ATmega8/kiterf/project/code/ESP32/Demo/components/dsp/include/dsp_math.h

#pragma once

/* Compiler specific diagnostic adjustment */
#if   defined ( __CC_DSP )

#elif defined ( __DSPCC_VERSION ) && ( __DSPCC_VERSION >= 6010050 )

#elif defined ( __GNUC__ )
#pragma GCC diagnostic push
#pragma GCC diagnostic ignored "-Wsign-conversion"
#pragma GCC diagnostic ignored "-Wconversion"
#pragma GCC diagnostic ignored "-Wunused-parameter"

#elif defined ( __ICCDSP__ )

#elif defined ( __TI_DSP__ )

#elif defined ( __CSMC__ )

#elif defined ( __TASKING__ )

#else
#error Unknown compiler
#endif

#include "string.h"
#include "math.h"
#include "stdint.h"
#ifdef   __cplusplus
extern "C"
{
#endif


/**
 * @brief Macros required for reciprocal calculation in Normalized LMS
 */


#define INDEX_MASK         0x0000003F
#ifndef PI
#define PI               3.14159265358979f
#endif

/**
 * @brief Macros required for SINE and COSINE Fast math approximations
 */

#define FAST_MATH_TABLE_SIZE  512


/**
 * @brief Error status returned by some functions in the library.
 */

typedef enum {
    dsp_MATH_SUCCESS = 0,                /**< No error */
    dsp_MATH_ARGUMENT_ERROR = -1,        /**< One or more arguments are incorrect */
    dsp_MATH_LENGTH_ERROR = -2,          /**< Length of data buffer is incorrect */
    dsp_MATH_SIZE_MISMATCH = -3,         /**< Size of matrices is not compatible with the operation. */
    dsp_MATH_NANINF = -4,                /**< Not-a-number (NaN) or infinity is generated */
    dsp_MATH_SINGULAR = -5,              /**< Generated by matrix inversion if the input matrix is singular and cannot be inverted. */
    dsp_MATH_TEST_FAILURE = -6           /**< Test Failed  */
} dsp_status;


/**
 * @brief 32-bit floating-point type definition.
 */
typedef float float32_t;

/**
 * @brief Instance structure for the floating-point FIR filter.
 */
typedef struct {
    uint16_t numTaps;     /**< number of filter coefficients in the filter. */
    float32_t *pState;    /**< points to the state variable array. The array is of length numTaps+blockSize-1. */
    float32_t *pCoeffs;   /**< points to the coefficient array. The array is of length numTaps. */
} dsp_fir_instance_f32;





/**
 * @brief Processing function for the floating-point FIR filter.
 * @param[in]  S          points to an instance of the floating-point FIR structure.
 * @param[in]  pSrc       points to the block of input data.
 * @param[out] pDst       points to the block of output data.
 * @param[in]  blockSize  number of samples to process.
 */
void dsp_fir_f32(
    const dsp_fir_instance_f32 *S,
    float32_t *pSrc,
    float32_t *pDst,
    uint32_t blockSize);


/**
 * @brief  Initialization function for the floating-point FIR filter.
 * @param[in,out] S          points to an instance of the floating-point FIR filter structure.
 * @param[in]     numTaps    Number of filter coefficients in the filter.
 * @param[in]     pCoeffs    points to the filter coefficients.
 * @param[in]     pState     points to the state buffer.
 * @param[in]     blockSize  number of samples that are processed at a time.
 */
void dsp_fir_init_f32(
    dsp_fir_instance_f32 *S,
    uint16_t numTaps,
    float32_t *pCoeffs,
    float32_t *pState,
    uint32_t blockSize);




/**
 * @brief Instance structure for the floating-point Biquad cascade filter.
 */
typedef struct {
    uint32_t numStages;      /**< number of 2nd order stages in the filter.  Overall order is 2*numStages. */
    float32_t *pState;       /**< Points to the array of state coefficients.  The array is of length 4*numStages. */
    float32_t *pCoeffs;      /**< Points to the array of coefficients.  The array is of length 5*numStages. */
} dsp_biquad_casd_df1_inst_f32;





/**
 * @brief Processing function for the floating-point Biquad cascade filter.
 * @param[in]  S          points to an instance of the floating-point Biquad cascade structure.
 * @param[in]  pSrc       points to the block of input data.
 * @param[out] pDst       points to the block of output data.
 * @param[in]  blockSize  number of samples to process.
 */
void dsp_biquad_cascade_df1_f32(
    const dsp_biquad_casd_df1_inst_f32 *S,
    float32_t *pSrc,
    float32_t *pDst,
    uint32_t blockSize);


/**
 * @brief  Initialization function for the floating-point Biquad cascade filter.
 * @param[in,out] S          points to an instance of the floating-point Biquad cascade structure.
 * @param[in]     numStages  number of 2nd order stages in the filter.
 * @param[in]     pCoeffs    points to the filter coefficients.
 * @param[in]     pState     points to the state buffer.
 */
void dsp_biquad_cascade_df1_init_f32(
    dsp_biquad_casd_df1_inst_f32 *S,
    uint8_t numStages,
    float32_t *pCoeffs,
    float32_t *pState);


/**
 * @brief Instance structure for the floating-point matrix structure.
 */
typedef struct {
    uint16_t numRows;     /**< number of rows of the matrix.     */
    uint16_t numCols;     /**< number of columns of the matrix.  */
    float32_t *pData;     /**< points to the data of the matrix. */
} dsp_matrix_instance_f32;







/**
 * @brief Floating-point matrix addition.
 * @param[in]  pSrcA  points to the first input matrix structure
 * @param[in]  pSrcB  points to the second input matrix structure
 * @param[out] pDst   points to output matrix structure
 * @return     The function returns either
 * <code>dsp_MATH_SIZE_MISMATCH</code> or <code>dsp_MATH_SUCCESS</code> based on the outcome of size checking.
 */
dsp_status dsp_mat_add_f32(
    const dsp_matrix_instance_f32 *pSrcA,
    const dsp_matrix_instance_f32 *pSrcB,
    dsp_matrix_instance_f32 *pDst);





/**
 * @brief Floating-point, complex, matrix multiplication.
 * @param[in]  pSrcA  points to the first input matrix structure
 * @param[in]  pSrcB  points to the second input matrix structure
 * @param[out] pDst   points to output matrix structure
 * @return     The function returns either
 * <code>dsp_MATH_SIZE_MISMATCH</code> or <code>dsp_MATH_SUCCESS</code> based on the outcome of size checking.
 */
dsp_status dsp_mat_cmplx_mult_f32(
    const dsp_matrix_instance_f32 *pSrcA,
    const dsp_matrix_instance_f32 *pSrcB,
    dsp_matrix_instance_f32 *pDst);




/**
 * @brief Floating-point matrix transpose.
 * @param[in]  pSrc  points to the input matrix
 * @param[out] pDst  points to the output matrix
 * @return    The function returns either  <code>dsp_MATH_SIZE_MISMATCH</code>
 * or <code>dsp_MATH_SUCCESS</code> based on the outcome of size checking.
 */
dsp_status dsp_mat_trans_f32(
    const dsp_matrix_instance_f32 *pSrc,
    dsp_matrix_instance_f32 *pDst);





/**
 * @brief Floating-point matrix multiplication
 * @param[in]  pSrcA  points to the first input matrix structure
 * @param[in]  pSrcB  points to the second input matrix structure
 * @param[out] pDst   points to output matrix structure
 * @return     The function returns either
 * <code>dsp_MATH_SIZE_MISMATCH</code> or <code>dsp_MATH_SUCCESS</code> based on the outcome of size checking.
 */
dsp_status dsp_mat_mult_f32(
    const dsp_matrix_instance_f32 *pSrcA,
    const dsp_matrix_instance_f32 *pSrcB,
    dsp_matrix_instance_f32 *pDst);





/**
 * @brief Floating-point matrix subtraction
 * @param[in]  pSrcA  points to the first input matrix structure
 * @param[in]  pSrcB  points to the second input matrix structure
 * @param[out] pDst   points to output matrix structure
 * @return     The function returns either
 * <code>dsp_MATH_SIZE_MISMATCH</code> or <code>dsp_MATH_SUCCESS</code> based on the outcome of size checking.
 */
dsp_status dsp_mat_sub_f32(
    const dsp_matrix_instance_f32 *pSrcA,
    const dsp_matrix_instance_f32 *pSrcB,
    dsp_matrix_instance_f32 *pDst);




/**
 * @brief Floating-point matrix scaling.
 * @param[in]  pSrc   points to the input matrix
 * @param[in]  scale  scale factor
 * @param[out] pDst   points to the output matrix
 * @return     The function returns either
 * <code>dsp_MATH_SIZE_MISMATCH</code> or <code>dsp_MATH_SUCCESS</code> based on the outcome of size checking.
 */
dsp_status dsp_mat_scale_f32(
    const dsp_matrix_instance_f32 *pSrc,
    float32_t scale,
    dsp_matrix_instance_f32 *pDst);





/**
 * @brief  Floating-point matrix initialization.
 * @param[in,out] S         points to an instance of the floating-point matrix structure.
 * @param[in]     nRows     number of rows in the matrix.
 * @param[in]     nColumns  number of columns in the matrix.
 * @param[in]     pData     points to the matrix data array.
 */
void dsp_mat_init_f32(
    dsp_matrix_instance_f32 *S,
    uint16_t nRows,
    uint16_t nColumns,
    float32_t *pData);




/**
 * @brief Instance structure for the floating-point PID Control.
 */
typedef struct {
    float32_t A0;          /**< The derived gain, A0 = Kp + Ki + Kd . */
    float32_t A1;          /**< The derived gain, A1 = -Kp - 2Kd. */
    float32_t A2;          /**< The derived gain, A2 = Kd . */
    float32_t state[3];    /**< The state array of length 3. */
    float32_t Kp;          /**< The proportional gain. */
    float32_t Ki;          /**< The integral gain. */
    float32_t Kd;          /**< The derivative gain. */
} dsp_pid_instance_f32;



/**
 * @brief  Initialization function for the floating-point PID Control.
 * @param[in,out] S               points to an instance of the PID structure.
 * @param[in]     resetStateFlag  flag to reset the state. 0 = no change in state 1 = reset the state.
 */
void dsp_pid_init_f32(
    dsp_pid_instance_f32 *S,
    int32_t resetStateFlag);


/**
 * @brief  Reset function for the floating-point PID Control.
 * @param[in,out] S  is an instance of the floating-point PID Control structure
 */
void dsp_pid_reset_f32(
    dsp_pid_instance_f32 *S);




/**
 * @brief Instance structure for the floating-point Linear Interpolate function.
 */
typedef struct {
    uint32_t nValues;           /**< nValues */
    float32_t x1;               /**< x1 */
    float32_t xSpacing;         /**< xSpacing */
    float32_t *pYData;          /**< pointer to the table of Y values */
} dsp_linear_interp_instance_f32;

/**
 * @brief Instance structure for the floating-point bilinear interpolation function.
 */
typedef struct {
    uint16_t numRows;   /**< number of rows in the data table. */
    uint16_t numCols;   /**< number of columns in the data table. */
    float32_t *pData;   /**< points to the data table. */
} dsp_bilinear_interp_instance_f32;

/**
* @brief Instance structure for the Q31 bilinear interpolation function.
*/










/**
 * @brief Floating-point vector multiplication.
 * @param[in]  pSrcA      points to the first input vector
 * @param[in]  pSrcB      points to the second input vector
 * @param[out] pDst       points to the output vector
 * @param[in]  blockSize  number of samples in each vector
 */
void dsp_mult_f32(
    float32_t *pSrcA,
    float32_t *pSrcB,
    float32_t *pDst,
    uint32_t blockSize);






/**
 * @brief Instance structure for the floating-point CFFT/CIFFT function.
 */
typedef struct {
    uint16_t fftLen;                   /**< length of the FFT. */
    uint8_t ifftFlag;                  /**< flag that selects forward (ifftFlag=0) or inverse (ifftFlag=1) transform. */
    uint8_t bitReverseFlag;            /**< flag that enables (bitReverseFlag=1) or disables (bitReverseFlag=0) bit reversal of output. */
    float32_t *pTwiddle;               /**< points to the Twiddle factor table. */
    uint16_t *pBitRevTable;            /**< points to the bit reversal table. */
    uint16_t twidCoefModifier;         /**< twiddle coefficient modifier that supports different size FFTs with the same twiddle factor table. */
    uint16_t bitRevFactor;             /**< bit reversal modifier that supports different size FFTs with the same bit reversal table. */
    float32_t onebyfftLen;             /**< value of 1/fftLen. */
} dsp_cfft_radix2_instance_f32;

/* Deprecated */
dsp_status dsp_cfft_radix2_init_f32(
    dsp_cfft_radix2_instance_f32 *S,
    uint16_t fftLen,
    uint8_t ifftFlag,
    uint8_t bitReverseFlag);

/* Deprecated */
void dsp_cfft_radix2_f32(
    const dsp_cfft_radix2_instance_f32 *S,
    float32_t *pSrc);

/**
 * @brief Instance structure for the floating-point CFFT/CIFFT function.
 */
typedef struct {
    uint16_t fftLen;                   /**< length of the FFT. */
    uint8_t ifftFlag;                  /**< flag that selects forward (ifftFlag=0) or inverse (ifftFlag=1) transform. */
    uint8_t bitReverseFlag;            /**< flag that enables (bitReverseFlag=1) or disables (bitReverseFlag=0) bit reversal of output. */
    float32_t *pTwiddle;               /**< points to the Twiddle factor table. */
    uint16_t *pBitRevTable;            /**< points to the bit reversal table. */
    uint16_t twidCoefModifier;         /**< twiddle coefficient modifier that supports different size FFTs with the same twiddle factor table. */
    uint16_t bitRevFactor;             /**< bit reversal modifier that supports different size FFTs with the same bit reversal table. */
    float32_t onebyfftLen;             /**< value of 1/fftLen. */
} dsp_cfft_radix4_instance_f32;

/* Deprecated */
dsp_status dsp_cfft_radix4_init_f32(
    dsp_cfft_radix4_instance_f32 *S,
    uint16_t fftLen,
    uint8_t ifftFlag,
    uint8_t bitReverseFlag);

/* Deprecated */
void dsp_cfft_radix4_f32(
    const dsp_cfft_radix4_instance_f32 *S,
    float32_t *pSrc);


/**
 * @brief Instance structure for the floating-point CFFT/CIFFT function.
 */
typedef struct {
    uint16_t fftLen;                   /**< length of the FFT. */
    const float32_t *pTwiddle;         /**< points to the Twiddle factor table. */
    const uint16_t *pBitRevTable;      /**< points to the bit reversal table. */
    uint16_t bitRevLength;             /**< bit reversal table length. */
} dsp_cfft_instance_f32;

void dsp_cfft_f32(
    const dsp_cfft_instance_f32 *S,
    float32_t *p1,
    uint8_t ifftFlag,
    uint8_t bitReverseFlag);





/**
 * @brief Instance structure for the floating-point RFFT/RIFFT function.
 */
typedef struct {
    uint32_t fftLenReal;                        /**< length of the real FFT. */
    uint16_t fftLenBy2;                         /**< length of the complex FFT. */
    uint8_t ifftFlagR;                          /**< flag that selects forward (ifftFlagR=0) or inverse (ifftFlagR=1) transform. */
    uint8_t bitReverseFlagR;                    /**< flag that enables (bitReverseFlagR=1) or disables (bitReverseFlagR=0) bit reversal of output. */
    uint32_t twidCoefRModifier;                     /**< twiddle coefficient modifier that supports different size FFTs with the same twiddle factor table. */
    float32_t *pTwiddleAReal;                   /**< points to the real twiddle factor table. */
    float32_t *pTwiddleBReal;                   /**< points to the imag twiddle factor table. */
    dsp_cfft_radix4_instance_f32 *pCfft;        /**< points to the complex FFT instance. */
} dsp_rfft_instance_f32;

dsp_status dsp_rfft_init_f32(
    dsp_rfft_instance_f32 *S,
    dsp_cfft_radix4_instance_f32 *S_CFFT,
    uint32_t fftLenReal,
    uint32_t ifftFlagR,
    uint32_t bitReverseFlag);

void dsp_rfft_f32(
    const dsp_rfft_instance_f32 *S,
    float32_t *pSrc,
    float32_t *pDst);

/**
 * @brief Instance structure for the floating-point RFFT/RIFFT function.
 */
typedef struct {
    dsp_cfft_instance_f32 Sint;      /**< Internal CFFT structure. */
    uint16_t fftLenRFFT;             /**< length of the real sequence */
    float32_t *pTwiddleRFFT;         /**< Twiddle factors real stage  */
} dsp_rfft_fast_instance_f32 ;

dsp_status dsp_rfft_fast_init_f32(
    dsp_rfft_fast_instance_f32 *S,
    uint16_t fftLen);

void dsp_rfft_fast_f32(
    dsp_rfft_fast_instance_f32 *S,
    float32_t *p, float32_t *pOut,
    uint8_t ifftFlag);

/**
 * @brief Instance structure for the floating-point DCT4/IDCT4 function.
 */
typedef struct {
    uint16_t N;                          /**< length of the DCT4. */
    uint16_t Nby2;                       /**< half of the length of the DCT4. */
    float32_t normalize;                 /**< normalizing factor. */
    float32_t *pTwiddle;                 /**< points to the twiddle factor table. */
    float32_t *pCosFactor;               /**< points to the cosFactor table. */
    dsp_rfft_instance_f32 *pRfft;        /**< points to the real FFT instance. */
    dsp_cfft_radix4_instance_f32 *pCfft; /**< points to the complex FFT instance. */
} dsp_dct4_instance_f32;


/**
 * @brief  Initialization function for the floating-point DCT4/IDCT4.
 * @param[in,out] S          points to an instance of floating-point DCT4/IDCT4 structure.
 * @param[in]     S_RFFT     points to an instance of floating-point RFFT/RIFFT structure.
 * @param[in]     S_CFFT     points to an instance of floating-point CFFT/CIFFT structure.
 * @param[in]     N          length of the DCT4.
 * @param[in]     Nby2       half of the length of the DCT4.
 * @param[in]     normalize  normalizing factor.
 * @return      dsp_status function returns dsp_MATH_SUCCESS if initialization is successful or dsp_MATH_ARGUMENT_ERROR if <code>fftLenReal</code> is not a supported transform length.
 */
dsp_status dsp_dct4_init_f32(
    dsp_dct4_instance_f32 *S,
    dsp_rfft_instance_f32 *S_RFFT,
    dsp_cfft_radix4_instance_f32 *S_CFFT,
    uint16_t N,
    uint16_t Nby2,
    float32_t normalize);


/**
 * @brief Processing function for the floating-point DCT4/IDCT4.
 * @param[in]     S              points to an instance of the floating-point DCT4/IDCT4 structure.
 * @param[in]     pState         points to state buffer.
 * @param[in,out] pInlineBuffer  points to the in-place input and output buffer.
 */
void dsp_dct4_f32(
    const dsp_dct4_instance_f32 *S,
    float32_t *pState,
    float32_t *pInlineBuffer);






/**
 * @brief Floating-point vector addition.
 * @param[in]  pSrcA      points to the first input vector
 * @param[in]  pSrcB      points to the second input vector
 * @param[out] pDst       points to the output vector
 * @param[in]  blockSize  number of samples in each vector
 */
void dsp_add_f32(
    float32_t *pSrcA,
    float32_t *pSrcB,
    float32_t *pDst,
    uint32_t blockSize);





/**
 * @brief Floating-point vector subtraction.
 * @param[in]  pSrcA      points to the first input vector
 * @param[in]  pSrcB      points to the second input vector
 * @param[out] pDst       points to the output vector
 * @param[in]  blockSize  number of samples in each vector
 */
void dsp_sub_f32(
    float32_t *pSrcA,
    float32_t *pSrcB,
    float32_t *pDst,
    uint32_t blockSize);





/**
 * @brief Multiplies a floating-point vector by a scalar.
 * @param[in]  pSrc       points to the input vector
 * @param[in]  scale      scale factor to be applied
 * @param[out] pDst       points to the output vector
 * @param[in]  blockSize  number of samples in the vector
 */
void dsp_scale_f32(
    float32_t *pSrc,
    float32_t scale,
    float32_t *pDst,
    uint32_t blockSize);





/**
 * @brief Floating-point vector absolute value.
 * @param[in]  pSrc       points to the input buffer
 * @param[out] pDst       points to the output buffer
 * @param[in]  blockSize  number of samples in each vector
 */
void dsp_abs_f32(
    float32_t *pSrc,
    float32_t *pDst,
    uint32_t blockSize);




/**
 * @brief Dot product of floating-point vectors.
 * @param[in]  pSrcA      points to the first input vector
 * @param[in]  pSrcB      points to the second input vector
 * @param[in]  blockSize  number of samples in each vector
 * @param[out] result     output result returned here
 */
void dsp_dot_prod_f32(
    float32_t *pSrcA,
    float32_t *pSrcB,
    uint32_t blockSize,
    float32_t *result);





/**
 * @brief  Adds a constant offset to a floating-point vector.
 * @param[in]  pSrc       points to the input vector
 * @param[in]  offset     is the offset to be added
 * @param[out] pDst       points to the output vector
 * @param[in]  blockSize  number of samples in the vector
 */
void dsp_offset_f32(
    float32_t *pSrc,
    float32_t offset,
    float32_t *pDst,
    uint32_t blockSize);




/**
 * @brief  Negates the elements of a floating-point vector.
 * @param[in]  pSrc       points to the input vector
 * @param[out] pDst       points to the output vector
 * @param[in]  blockSize  number of samples in the vector
 */
void dsp_negate_f32(
    float32_t *pSrc,
    float32_t *pDst,
    uint32_t blockSize);





/**
 * @brief  Copies the elements of a floating-point vector.
 * @param[in]  pSrc       input pointer
 * @param[out] pDst       output pointer
 * @param[in]  blockSize  number of samples to process
 */
void dsp_copy_f32(
    float32_t *pSrc,
    float32_t *pDst,
    uint32_t blockSize);





/**
 * @brief  Fills a constant value into a floating-point vector.
 * @param[in]  value      input value to be filled
 * @param[out] pDst       output pointer
 * @param[in]  blockSize  number of samples to process
 */
void dsp_fill_f32(
    float32_t value,
    float32_t *pDst,
    uint32_t blockSize);





/**
 * @brief Convolution of floating-point sequences.
 * @param[in]  pSrcA    points to the first input sequence.
 * @param[in]  srcALen  length of the first input sequence.
 * @param[in]  pSrcB    points to the second input sequence.
 * @param[in]  srcBLen  length of the second input sequence.
 * @param[out] pDst     points to the location where the output result is written.  Length srcALen+srcBLen-1.
 */
void dsp_conv_f32(
    float32_t *pSrcA,
    uint32_t srcALen,
    float32_t *pSrcB,
    uint32_t srcBLen,
    float32_t *pDst);





/**
 * @brief Partial convolution of floating-point sequences.
 * @param[in]  pSrcA       points to the first input sequence.
 * @param[in]  srcALen     length of the first input sequence.
 * @param[in]  pSrcB       points to the second input sequence.
 * @param[in]  srcBLen     length of the second input sequence.
 * @param[out] pDst        points to the block of output data
 * @param[in]  firstIndex  is the first output sample to start with.
 * @param[in]  numPoints   is the number of output points to be computed.
 * @return  Returns either dsp_MATH_SUCCESS if the function completed correctly or dsp_MATH_ARGUMENT_ERROR if the requested subset is not in the range [0 srcALen+srcBLen-2].
 */
dsp_status dsp_conv_partial_f32(
    float32_t *pSrcA,
    uint32_t srcALen,
    float32_t *pSrcB,
    uint32_t srcBLen,
    float32_t *pDst,
    uint32_t firstIndex,
    uint32_t numPoints);







/**
 * @brief Instance structure for the floating-point FIR decimator.
 */
typedef struct {
    uint8_t M;                  /**< decimation factor. */
    uint16_t numTaps;           /**< number of coefficients in the filter. */
    float32_t *pCoeffs;         /**< points to the coefficient array. The array is of length numTaps.*/
    float32_t *pState;          /**< points to the state variable array. The array is of length numTaps+blockSize-1. */
} dsp_fir_decimate_instance_f32;


/**
 * @brief Processing function for the floating-point FIR decimator.
 * @param[in]  S          points to an instance of the floating-point FIR decimator structure.
 * @param[in]  pSrc       points to the block of input data.
 * @param[out] pDst       points to the block of output data
 * @param[in]  blockSize  number of input samples to process per call.
 */
void dsp_fir_decimate_f32(
    const dsp_fir_decimate_instance_f32 *S,
    float32_t *pSrc,
    float32_t *pDst,
    uint32_t blockSize);


/**
 * @brief  Initialization function for the floating-point FIR decimator.
 * @param[in,out] S          points to an instance of the floating-point FIR decimator structure.
 * @param[in]     numTaps    number of coefficients in the filter.
 * @param[in]     M          decimation factor.
 * @param[in]     pCoeffs    points to the filter coefficients.
 * @param[in]     pState     points to the state buffer.
 * @param[in]     blockSize  number of input samples to process per call.
 * @return    The function returns dsp_MATH_SUCCESS if initialization is successful or dsp_MATH_LENGTH_ERROR if
 * <code>blockSize</code> is not a multiple of <code>M</code>.
 */
dsp_status dsp_fir_decimate_init_f32(
    dsp_fir_decimate_instance_f32 *S,
    uint16_t numTaps,
    uint8_t M,
    float32_t *pCoeffs,
    float32_t *pState,
    uint32_t blockSize);






/**
 * @brief Instance structure for the floating-point FIR interpolator.
 */
typedef struct {
    uint8_t L;                     /**< upsample factor. */
    uint16_t phaseLength;          /**< length of each polyphase filter component. */
    float32_t *pCoeffs;            /**< points to the coefficient array. The array is of length L*phaseLength. */
    float32_t *pState;             /**< points to the state variable array. The array is of length phaseLength+numTaps-1. */
} dsp_fir_interpolate_instance_f32;





/**
 * @brief Processing function for the floating-point FIR interpolator.
 * @param[in]  S          points to an instance of the floating-point FIR interpolator structure.
 * @param[in]  pSrc       points to the block of input data.
 * @param[out] pDst       points to the block of output data.
 * @param[in]  blockSize  number of input samples to process per call.
 */
void dsp_fir_interpolate_f32(
    const dsp_fir_interpolate_instance_f32 *S,
    float32_t *pSrc,
    float32_t *pDst,
    uint32_t blockSize);


/**
 * @brief  Initialization function for the floating-point FIR interpolator.
 * @param[in,out] S          points to an instance of the floating-point FIR interpolator structure.
 * @param[in]     L          upsample factor.
 * @param[in]     numTaps    number of filter coefficients in the filter.
 * @param[in]     pCoeffs    points to the filter coefficient buffer.
 * @param[in]     pState     points to the state buffer.
 * @param[in]     blockSize  number of input samples to process per call.
 * @return        The function returns dsp_MATH_SUCCESS if initialization is successful or dsp_MATH_LENGTH_ERROR if
 * the filter length <code>numTaps</code> is not a multiple of the interpolation factor <code>L</code>.
 */
dsp_status dsp_fir_interpolate_init_f32(
    dsp_fir_interpolate_instance_f32 *S,
    uint8_t L,
    uint16_t numTaps,
    float32_t *pCoeffs,
    float32_t *pState,
    uint32_t blockSize);





/**
 * @brief Instance structure for the floating-point transposed direct form II Biquad cascade filter.
 */
typedef struct {
    uint8_t numStages;         /**< number of 2nd order stages in the filter.  Overall order is 2*numStages. */
    float32_t *pState;         /**< points to the array of state coefficients.  The array is of length 2*numStages. */
    float32_t *pCoeffs;        /**< points to the array of coefficients.  The array is of length 5*numStages. */
} dsp_biquad_cascade_df2T_instance_f32;

/**
 * @brief Instance structure for the floating-point transposed direct form II Biquad cascade filter.
 */
typedef struct {
    uint8_t numStages;         /**< number of 2nd order stages in the filter.  Overall order is 2*numStages. */
    float32_t *pState;         /**< points to the array of state coefficients.  The array is of length 4*numStages. */
    float32_t *pCoeffs;        /**< points to the array of coefficients.  The array is of length 5*numStages. */
} dsp_biquad_cascade_stereo_df2T_instance_f32;




/**
 * @brief Processing function for the floating-point transposed direct form II Biquad cascade filter.
 * @param[in]  S          points to an instance of the filter data structure.
 * @param[in]  pSrc       points to the block of input data.
 * @param[out] pDst       points to the block of output data
 * @param[in]  blockSize  number of samples to process.
 */
void dsp_biquad_cascade_df2T_f32(
    const dsp_biquad_cascade_df2T_instance_f32 *S,
    float32_t *pSrc,
    float32_t *pDst,
    uint32_t blockSize);


/**
 * @brief Processing function for the floating-point transposed direct form II Biquad cascade filter. 2 channels
 * @param[in]  S          points to an instance of the filter data structure.
 * @param[in]  pSrc       points to the block of input data.
 * @param[out] pDst       points to the block of output data
 * @param[in]  blockSize  number of samples to process.
 */
void dsp_biquad_cascade_stereo_df2T_f32(
    const dsp_biquad_cascade_stereo_df2T_instance_f32 *S,
    float32_t *pSrc,
    float32_t *pDst,
    uint32_t blockSize);





/**
 * @brief  Initialization function for the floating-point transposed direct form II Biquad cascade filter.
 * @param[in,out] S          points to an instance of the filter data structure.
 * @param[in]     numStages  number of 2nd order stages in the filter.
 * @param[in]     pCoeffs    points to the filter coefficients.
 * @param[in]     pState     points to the state buffer.
 */
void dsp_biquad_cascade_df2T_init_f32(
    dsp_biquad_cascade_df2T_instance_f32 *S,
    uint8_t numStages,
    float32_t *pCoeffs,
    float32_t *pState);


/**
 * @brief  Initialization function for the floating-point transposed direct form II Biquad cascade filter.
 * @param[in,out] S          points to an instance of the filter data structure.
 * @param[in]     numStages  number of 2nd order stages in the filter.
 * @param[in]     pCoeffs    points to the filter coefficients.
 * @param[in]     pState     points to the state buffer.
 */
void dsp_biquad_cascade_stereo_df2T_init_f32(
    dsp_biquad_cascade_stereo_df2T_instance_f32 *S,
    uint8_t numStages,
    float32_t *pCoeffs,
    float32_t *pState);





/**
 * @brief Instance structure for the floating-point FIR lattice filter.
 */
typedef struct {
    uint16_t numStages;                  /**< number of filter stages. */
    float32_t *pState;                   /**< points to the state variable array. The array is of length numStages. */
    float32_t *pCoeffs;                  /**< points to the coefficient array. The array is of length numStages. */
} dsp_fir_lattice_instance_f32;




/**
 * @brief Initialization function for the floating-point FIR lattice filter.
 * @param[in] S          points to an instance of the floating-point FIR lattice structure.
 * @param[in] numStages  number of filter stages.
 * @param[in] pCoeffs    points to the coefficient buffer.  The array is of length numStages.
 * @param[in] pState     points to the state buffer.  The array is of length numStages.
 */
void dsp_fir_lattice_init_f32(
    dsp_fir_lattice_instance_f32 *S,
    uint16_t numStages,
    float32_t *pCoeffs,
    float32_t *pState);


/**
 * @brief Processing function for the floating-point FIR lattice filter.
 * @param[in]  S          points to an instance of the floating-point FIR lattice structure.
 * @param[in]  pSrc       points to the block of input data.
 * @param[out] pDst       points to the block of output data
 * @param[in]  blockSize  number of samples to process.
 */
void dsp_fir_lattice_f32(
    const dsp_fir_lattice_instance_f32 *S,
    float32_t *pSrc,
    float32_t *pDst,
    uint32_t blockSize);



/**
 * @brief Instance structure for the floating-point IIR lattice filter.
 */
typedef struct {
    uint16_t numStages;                  /**< number of stages in the filter. */
    float32_t *pState;                   /**< points to the state variable array. The array is of length numStages+blockSize. */
    float32_t *pkCoeffs;                 /**< points to the reflection coefficient array. The array is of length numStages. */
    float32_t *pvCoeffs;                 /**< points to the ladder coefficient array. The array is of length numStages+1. */
} dsp_iir_lattice_instance_f32;


/**
 * @brief Processing function for the floating-point IIR lattice filter.
 * @param[in]  S          points to an instance of the floating-point IIR lattice structure.
 * @param[in]  pSrc       points to the block of input data.
 * @param[out] pDst       points to the block of output data.
 * @param[in]  blockSize  number of samples to process.
 */
void dsp_iir_lattice_f32(
    const dsp_iir_lattice_instance_f32 *S,
    float32_t *pSrc,
    float32_t *pDst,
    uint32_t blockSize);


/**
 * @brief Initialization function for the floating-point IIR lattice filter.
 * @param[in] S          points to an instance of the floating-point IIR lattice structure.
 * @param[in] numStages  number of stages in the filter.
 * @param[in] pkCoeffs   points to the reflection coefficient buffer.  The array is of length numStages.
 * @param[in] pvCoeffs   points to the ladder coefficient buffer.  The array is of length numStages+1.
 * @param[in] pState     points to the state buffer.  The array is of length numStages+blockSize-1.
 * @param[in] blockSize  number of samples to process.
 */
void dsp_iir_lattice_init_f32(
    dsp_iir_lattice_instance_f32 *S,
    uint16_t numStages,
    float32_t *pkCoeffs,
    float32_t *pvCoeffs,
    float32_t *pState,
    uint32_t blockSize);





/**
 * @brief Instance structure for the floating-point LMS filter.
 */
typedef struct {
    uint16_t numTaps;    /**< number of coefficients in the filter. */
    float32_t *pState;   /**< points to the state variable array. The array is of length numTaps+blockSize-1. */
    float32_t *pCoeffs;  /**< points to the coefficient array. The array is of length numTaps. */
    float32_t mu;        /**< step size that controls filter coefficient updates. */
} dsp_lms_instance_f32;


/**
 * @brief Processing function for floating-point LMS filter.
 * @param[in]  S          points to an instance of the floating-point LMS filter structure.
 * @param[in]  pSrc       points to the block of input data.
 * @param[in]  pRef       points to the block of reference data.
 * @param[out] pOut       points to the block of output data.
 * @param[out] pErr       points to the block of error data.
 * @param[in]  blockSize  number of samples to process.
 */
void dsp_lms_f32(
    const dsp_lms_instance_f32 *S,
    float32_t *pSrc,
    float32_t *pRef,
    float32_t *pOut,
    float32_t *pErr,
    uint32_t blockSize);


/**
 * @brief Initialization function for floating-point LMS filter.
 * @param[in] S          points to an instance of the floating-point LMS filter structure.
 * @param[in] numTaps    number of filter coefficients.
 * @param[in] pCoeffs    points to the coefficient buffer.
 * @param[in] pState     points to state buffer.
 * @param[in] mu         step size that controls filter coefficient updates.
 * @param[in] blockSize  number of samples to process.
 */
void dsp_lms_init_f32(
    dsp_lms_instance_f32 *S,
    uint16_t numTaps,
    float32_t *pCoeffs,
    float32_t *pState,
    float32_t mu,
    uint32_t blockSize);








/**
 * @brief Instance structure for the floating-point normalized LMS filter.
 */
typedef struct {
    uint16_t numTaps;     /**< number of coefficients in the filter. */
    float32_t *pState;    /**< points to the state variable array. The array is of length numTaps+blockSize-1. */
    float32_t *pCoeffs;   /**< points to the coefficient array. The array is of length numTaps. */
    float32_t mu;         /**< step size that control filter coefficient updates. */
    float32_t energy;     /**< saves previous frame energy. */
    float32_t x0;         /**< saves previous input sample. */
} dsp_lms_norm_instance_f32;


/**
 * @brief Processing function for floating-point normalized LMS filter.
 * @param[in]  S          points to an instance of the floating-point normalized LMS filter structure.
 * @param[in]  pSrc       points to the block of input data.
 * @param[in]  pRef       points to the block of reference data.
 * @param[out] pOut       points to the block of output data.
 * @param[out] pErr       points to the block of error data.
 * @param[in]  blockSize  number of samples to process.
 */
void dsp_lms_norm_f32(
    dsp_lms_norm_instance_f32 *S,
    float32_t *pSrc,
    float32_t *pRef,
    float32_t *pOut,
    float32_t *pErr,
    uint32_t blockSize);


/**
 * @brief Initialization function for floating-point normalized LMS filter.
 * @param[in] S          points to an instance of the floating-point LMS filter structure.
 * @param[in] numTaps    number of filter coefficients.
 * @param[in] pCoeffs    points to coefficient buffer.
 * @param[in] pState     points to state buffer.
 * @param[in] mu         step size that controls filter coefficient updates.
 * @param[in] blockSize  number of samples to process.
 */
void dsp_lms_norm_init_f32(
    dsp_lms_norm_instance_f32 *S,
    uint16_t numTaps,
    float32_t *pCoeffs,
    float32_t *pState,
    float32_t mu,
    uint32_t blockSize);




/**
 * @brief Correlation of floating-point sequences.
 * @param[in]  pSrcA    points to the first input sequence.
 * @param[in]  srcALen  length of the first input sequence.
 * @param[in]  pSrcB    points to the second input sequence.
 * @param[in]  srcBLen  length of the second input sequence.
 * @param[out] pDst     points to the block of output data  Length 2 * max(srcALen, srcBLen) - 1.
 */
void dsp_correlate_f32(
    float32_t *pSrcA,
    uint32_t srcALen,
    float32_t *pSrcB,
    uint32_t srcBLen,
    float32_t *pDst);





/**
 * @brief Instance structure for the floating-point sparse FIR filter.
 */
typedef struct {
    uint16_t numTaps;             /**< number of coefficients in the filter. */
    uint16_t stateIndex;          /**< state buffer index.  Points to the oldest sample in the state buffer. */
    float32_t *pState;            /**< points to the state buffer array. The array is of length maxDelay+blockSize-1. */
    float32_t *pCoeffs;           /**< points to the coefficient array. The array is of length numTaps.*/
    uint16_t maxDelay;            /**< maximum offset specified by the pTapDelay array. */
    int32_t *pTapDelay;           /**< points to the array of delay values.  The array is of length numTaps. */
} dsp_fir_sparse_instance_f32;







/**
 * @brief Processing function for the floating-point sparse FIR filter.
 * @param[in]  S           points to an instance of the floating-point sparse FIR structure.
 * @param[in]  pSrc        points to the block of input data.
 * @param[out] pDst        points to the block of output data
 * @param[in]  pScratchIn  points to a temporary buffer of size blockSize.
 * @param[in]  blockSize   number of input samples to process per call.
 */
void dsp_fir_sparse_f32(
    dsp_fir_sparse_instance_f32 *S,
    float32_t *pSrc,
    float32_t *pDst,
    float32_t *pScratchIn,
    uint32_t blockSize);


/**
 * @brief  Initialization function for the floating-point sparse FIR filter.
 * @param[in,out] S          points to an instance of the floating-point sparse FIR structure.
 * @param[in]     numTaps    number of nonzero coefficients in the filter.
 * @param[in]     pCoeffs    points to the array of filter coefficients.
 * @param[in]     pState     points to the state buffer.
 * @param[in]     pTapDelay  points to the array of offset times.
 * @param[in]     maxDelay   maximum offset time supported.
 * @param[in]     blockSize  number of samples that will be processed per block.
 */
void dsp_fir_sparse_init_f32(
    dsp_fir_sparse_instance_f32 *S,
    uint16_t numTaps,
    float32_t *pCoeffs,
    float32_t *pState,
    int32_t *pTapDelay,
    uint16_t maxDelay,
    uint32_t blockSize);




/**
 * @brief  Floating-point sin_cos function.
 * @param[in]  theta   input value in degrees
 * @param[out] pSinVal  points to the processed sine output.
 * @param[out] pCosVal  points to the processed cos output.
 */
void dsp_sin_cos_f32(
    float32_t theta,
    float32_t *pSinVal,
    float32_t *pCosVal);




/**
 * @brief  Floating-point complex conjugate.
 * @param[in]  pSrc        points to the input vector
 * @param[out] pDst        points to the output vector
 * @param[in]  numSamples  number of complex samples in each vector
 */
void dsp_cmplx_conj_f32(
    float32_t *pSrc,
    float32_t *pDst,
    uint32_t numSamples);







/**
 * @brief  Floating-point complex magnitude squared
 * @param[in]  pSrc        points to the complex input vector
 * @param[out] pDst        points to the real output vector
 * @param[in]  numSamples  number of complex samples in the input vector
 */
void dsp_cmplx_mag_squared_f32(
    float32_t *pSrc,
    float32_t *pDst,
    uint32_t numSamples);




/**
  * @ingroup groupController
  */

/**
 * @defgroup PID PID Motor Control
 *
 * A Proportional Integral Derivative (PID) controller is a generic feedback control
 * loop mechanism widely used in industrial control systems.
 * A PID controller is the most commonly used type of feedback controller.
 *
 * This set of functions implements (PID) controllers
 * for Q15, Q31, and floating-point data types.  The functions operate on a single sample
 * of data and each call to the function returns a single processed value.
 * <code>S</code> points to an instance of the PID control data structure.  <code>in</code>
 * is the input sample value. The functions return the output value.
 *
 * \par Algorithm:
 * <pre>
 *    y[n] = y[n-1] + A0 * x[n] + A1 * x[n-1] + A2 * x[n-2]
 *    A0 = Kp + Ki + Kd
 *    A1 = (-Kp ) - (2 * Kd )
 *    A2 = Kd  </pre>
 *
 * \par
 * where \c Kp is proportional constant, \c Ki is Integral constant and \c Kd is Derivative constant
 *
 * \par
 * \image html PID.gif "Proportional Integral Derivative Controller"
 *
 * \par
 * The PID controller calculates an "error" value as the difference between
 * the measured output and the reference input.
 * The controller attempts to minimize the error by adjusting the process control inputs.
 * The proportional value determines the reaction to the current error,
 * the integral value determines the reaction based on the sum of recent errors,
 * and the derivative value determines the reaction based on the rate at which the error has been changing.
 *
 * \par Instance Structure
 * The Gains A0, A1, A2 and state variables for a PID controller are stored together in an instance data structure.
 * A separate instance structure must be defined for each PID Controller.
 * There are separate instance structure declarations for each of the 3 supported data types.
 *
 * \par Reset Functions
 * There is also an associated reset function for each data type which clears the state array.
 *
 * \par Initialization Functions
 * There is also an associated initialization function for each data type.
 * The initialization function performs the following operations:
 * - Initializes the Gains A0, A1, A2 from Kp,Ki, Kd gains.
 * - Zeros out the values in the state buffer.
 *
 * \par
 * Instance structure cannot be placed into a const data section and it is recommended to use the initialization function.
 *
 * \par Fixed-Point Behavior
 * Care must be taken when using the fixed-point versions of the PID Controller functions.
 * In particular, the overflow and saturation behavior of the accumulator used in each function must be considered.
 * Refer to the function specific documentation below for usage guidelines.
 */

/**
 * @addtogroup PID
 * @{
 */

/**
 * @brief  Process function for the floating-point PID Control.
 * @param[in,out] S   is an instance of the floating-point PID Control structure
 * @param[in]     in  input sample to process
 * @return out processed output sample.
 */
static inline float32_t dsp_pid_f32(
    dsp_pid_instance_f32 *S,
    float32_t in)
{
    float32_t out;

    /* y[n] = y[n-1] + A0 * x[n] + A1 * x[n-1] + A2 * x[n-2]  */
    out = (S->A0 * in) +
          (S->A1 * S->state[0]) + (S->A2 * S->state[1]) + (S->state[2]);

    /* Update state */
    S->state[1] = S->state[0];
    S->state[0] = in;
    S->state[2] = out;

    /* return to application */
    return (out);

}






/**
 * @} end of PID group
 */


/**
 * @brief Floating-point matrix inverse.
 * @param[in]  src   points to the instance of the input floating-point matrix structure.
 * @param[out] dst   points to the instance of the output floating-point matrix structure.
 * @return The function returns dsp_MATH_SIZE_MISMATCH, if the dimensions do not match.
 * If the input matrix is singular (does not have an inverse), then the algorithm terminates and returns error status dsp_MATH_SINGULAR.
 */
dsp_status dsp_mat_inverse_f32(
    const dsp_matrix_instance_f32 *src,
    dsp_matrix_instance_f32 *dst);






/**
 * @ingroup groupController
 */

/**
 * @defgroup clarke Vector Clarke Transform
 * Forward Clarke transform converts the instantaneous stator phases into a two-coordinate time invariant vector.
 * Generally the Clarke transform uses three-phase currents <code>Ia, Ib and Ic</code> to calculate currents
 * in the two-phase orthogonal stator axis <code>Ialpha</code> and <code>Ibeta</code>.
 * When <code>Ialpha</code> is superposed with <code>Ia</code> as shown in the figure below
 * \image html clarke.gif Stator current space vector and its components in (a,b).
 * and <code>Ia + Ib + Ic = 0</code>, in this condition <code>Ialpha</code> and <code>Ibeta</code>
 * can be calculated using only <code>Ia</code> and <code>Ib</code>.
 *
 * The function operates on a single sample of data and each call to the function returns the processed output.
 * The library provides separate functions for Q31 and floating-point data types.
 * \par Algorithm
 * \image html clarkeFormula.gif
 * where <code>Ia</code> and <code>Ib</code> are the instantaneous stator phases and
 * <code>pIalpha</code> and <code>pIbeta</code> are the two coordinates of time invariant vector.
 * \par Fixed-Point Behavior
 * Care must be taken when using the Q31 version of the Clarke transform.
 * In particular, the overflow and saturation behavior of the accumulator used must be considered.
 * Refer to the function specific documentation below for usage guidelines.
 */

/**
 * @addtogroup clarke
 * @{
 */

/**
 *
 * @brief  Floating-point Clarke transform
 * @param[in]  Ia       input three-phase coordinate <code>a</code>
 * @param[in]  Ib       input three-phase coordinate <code>b</code>
 * @param[out] pIalpha  points to output two-phase orthogonal vector axis alpha
 * @param[out] pIbeta   points to output two-phase orthogonal vector axis beta
 */
static inline void dsp_clarke_f32(
    float32_t Ia,
    float32_t Ib,
    float32_t *pIalpha,
    float32_t *pIbeta)
{
    /* Calculate pIalpha using the equation, pIalpha = Ia */
    *pIalpha = Ia;

    /* Calculate pIbeta using the equation, pIbeta = (1/sqrt(3)) * Ia + (2/sqrt(3)) * Ib */
    *pIbeta = ((float32_t) 0.57735026919 * Ia + (float32_t) 1.15470053838 * Ib);
}




/**
 * @ingroup groupController
 */

/**
 * @defgroup inv_clarke Vector Inverse Clarke Transform
 * Inverse Clarke transform converts the two-coordinate time invariant vector into instantaneous stator phases.
 *
 * The function operates on a single sample of data and each call to the function returns the processed output.
 * The library provides separate functions for Q31 and floating-point data types.
 * \par Algorithm
 * \image html clarkeInvFormula.gif
 * where <code>pIa</code> and <code>pIb</code> are the instantaneous stator phases and
 * <code>Ialpha</code> and <code>Ibeta</code> are the two coordinates of time invariant vector.
 * \par Fixed-Point Behavior
 * Care must be taken when using the Q31 version of the Clarke transform.
 * In particular, the overflow and saturation behavior of the accumulator used must be considered.
 * Refer to the function specific documentation below for usage guidelines.
 */

/**
 * @addtogroup inv_clarke
 * @{
 */

/**
* @brief  Floating-point Inverse Clarke transform
* @param[in]  Ialpha  input two-phase orthogonal vector axis alpha
* @param[in]  Ibeta   input two-phase orthogonal vector axis beta
* @param[out] pIa     points to output three-phase coordinate <code>a</code>
* @param[out] pIb     points to output three-phase coordinate <code>b</code>
*/
static inline void dsp_inv_clarke_f32(
    float32_t Ialpha,
    float32_t Ibeta,
    float32_t *pIa,
    float32_t *pIb)
{
    /* Calculating pIa from Ialpha by equation pIa = Ialpha */
    *pIa = Ialpha;

    /* Calculating pIb from Ialpha and Ibeta by equation pIb = -(1/2) * Ialpha + (sqrt(3)/2) * Ibeta */
    *pIb = -0.5f * Ialpha + 0.8660254039f * Ibeta;
}






/**
 * @ingroup groupController
 */

/**
 * @defgroup park Vector Park Transform
 *
 * Forward Park transform converts the input two-coordinate vector to flux and torque components.
 * The Park transform can be used to realize the transformation of the <code>Ialpha</code> and the <code>Ibeta</code> currents
 * from the stationary to the moving reference frame and control the spatial relationship between
 * the stator vector current and rotor flux vector.
 * If we consider the d axis aligned with the rotor flux, the diagram below shows the
 * current vector and the relationship from the two reference frames:
 * \image html park.gif "Stator current space vector and its component in (a,b) and in the d,q rotating reference frame"
 *
 * The function operates on a single sample of data and each call to the function returns the processed output.
 * The library provides separate functions for Q31 and floating-point data types.
 * \par Algorithm
 * \image html parkFormula.gif
 * where <code>Ialpha</code> and <code>Ibeta</code> are the stator vector components,
 * <code>pId</code> and <code>pIq</code> are rotor vector components and <code>cosVal</code> and <code>sinVal</code> are the
 * cosine and sine values of theta (rotor flux position).
 * \par Fixed-Point Behavior
 * Care must be taken when using the Q31 version of the Park transform.
 * In particular, the overflow and saturation behavior of the accumulator used must be considered.
 * Refer to the function specific documentation below for usage guidelines.
 */

/**
 * @addtogroup park
 * @{
 */

/**
 * @brief Floating-point Park transform
 * @param[in]  Ialpha  input two-phase vector coordinate alpha
 * @param[in]  Ibeta   input two-phase vector coordinate beta
 * @param[out] pId     points to output   rotor reference frame d
 * @param[out] pIq     points to output   rotor reference frame q
 * @param[in]  sinVal  sine value of rotation angle theta
 * @param[in]  cosVal  cosine value of rotation angle theta
 *
 * The function implements the forward Park transform.
 *
 */
static inline void dsp_park_f32(
    float32_t Ialpha,
    float32_t Ibeta,
    float32_t *pId,
    float32_t *pIq,
    float32_t sinVal,
    float32_t cosVal)
{
    /* Calculate pId using the equation, pId = Ialpha * cosVal + Ibeta * sinVal */
    *pId = Ialpha * cosVal + Ibeta * sinVal;

    /* Calculate pIq using the equation, pIq = - Ialpha * sinVal + Ibeta * cosVal */
    *pIq = -Ialpha * sinVal + Ibeta * cosVal;
}





/**
 * @ingroup groupController
 */

/**
 * @defgroup inv_park Vector Inverse Park transform
 * Inverse Park transform converts the input flux and torque components to two-coordinate vector.
 *
 * The function operates on a single sample of data and each call to the function returns the processed output.
 * The library provides separate functions for Q31 and floating-point data types.
 * \par Algorithm
 * \image html parkInvFormula.gif
 * where <code>pIalpha</code> and <code>pIbeta</code> are the stator vector components,
 * <code>Id</code> and <code>Iq</code> are rotor vector components and <code>cosVal</code> and <code>sinVal</code> are the
 * cosine and sine values of theta (rotor flux position).
 * \par Fixed-Point Behavior
 * Care must be taken when using the Q31 version of the Park transform.
 * In particular, the overflow and saturation behavior of the accumulator used must be considered.
 * Refer to the function specific documentation below for usage guidelines.
 */

/**
 * @addtogroup inv_park
 * @{
 */

/**
* @brief  Floating-point Inverse Park transform
* @param[in]  Id       input coordinate of rotor reference frame d
* @param[in]  Iq       input coordinate of rotor reference frame q
* @param[out] pIalpha  points to output two-phase orthogonal vector axis alpha
* @param[out] pIbeta   points to output two-phase orthogonal vector axis beta
* @param[in]  sinVal   sine value of rotation angle theta
* @param[in]  cosVal   cosine value of rotation angle theta
*/
static inline void dsp_inv_park_f32(
    float32_t Id,
    float32_t Iq,
    float32_t *pIalpha,
    float32_t *pIbeta,
    float32_t sinVal,
    float32_t cosVal)
{
    /* Calculate pIalpha using the equation, pIalpha = Id * cosVal - Iq * sinVal */
    *pIalpha = Id * cosVal - Iq * sinVal;

    /* Calculate pIbeta using the equation, pIbeta = Id * sinVal + Iq * cosVal */
    *pIbeta = Id * sinVal + Iq * cosVal;
}








/**
 * @ingroup groupInterpolation
 */

/**
 * @defgroup LinearInterpolate Linear Interpolation
 *
 * Linear interpolation is a method of curve fitting using linear polynomials.
 * Linear interpolation works by effectively drawing a straight line between two neighboring samples and returning the appropriate point along that line
 *
 * \par
 * \image html LinearInterp.gif "Linear interpolation"
 *
 * \par
 * A  Linear Interpolate function calculates an output value(y), for the input(x)
 * using linear interpolation of the input values x0, x1( nearest input values) and the output values y0 and y1(nearest output values)
 *
 * \par Algorithm:
 * <pre>
 *       y = y0 + (x - x0) * ((y1 - y0)/(x1-x0))
 *       where x0, x1 are nearest values of input x
 *             y0, y1 are nearest values to output y
 * </pre>
 *
 * \par
 * This set of functions implements Linear interpolation process
 * for Q7, Q15, Q31, and floating-point data types.  The functions operate on a single
 * sample of data and each call to the function returns a single processed value.
 * <code>S</code> points to an instance of the Linear Interpolate function data structure.
 * <code>x</code> is the input sample value. The functions returns the output value.
 *
 * \par
 * if x is outside of the table boundary, Linear interpolation returns first value of the table
 * if x is below input range and returns last value of table if x is above range.
 */

/**
 * @addtogroup LinearInterpolate
 * @{
 */

/**
 * @brief  Process function for the floating-point Linear Interpolation Function.
 * @param[in,out] S  is an instance of the floating-point Linear Interpolation structure
 * @param[in]     x  input sample to process
 * @return y processed output sample.
 *
 */
static inline float32_t dsp_linear_interp_f32(
    dsp_linear_interp_instance_f32 *S,
    float32_t x)
{
    float32_t y;
    float32_t x0, x1;                            /* Nearest input values */
    float32_t y0, y1;                            /* Nearest output values */
    float32_t xSpacing = S->xSpacing;            /* spacing between input values */
    int32_t i;                                   /* Index variable */
    float32_t *pYData = S->pYData;               /* pointer to output table */

    /* Calculation of index */
    i = (int32_t)((x - S->x1) / xSpacing);

    if (i < 0) {
        /* Iniatilize output for below specified range as least output value of table */
        y = pYData[0];
    } else if ((uint32_t)i >= S->nValues) {
        /* Iniatilize output for above specified range as last output value of table */
        y = pYData[S->nValues - 1];
    } else {
        /* Calculation of nearest input values */
        x0 = S->x1 +  i      * xSpacing;
        x1 = S->x1 + (i + 1) * xSpacing;

        /* Read of nearest output values */
        y0 = pYData[i];
        y1 = pYData[i + 1];

        /* Calculation of output */
        y = y0 + (x - x0) * ((y1 - y0) / (x1 - x0));

    }

    /* returns output value */
    return (y);
}





/**
 * @} end of LinearInterpolate group
 */

/**
 * @brief  Fast approximation to the trigonometric sine function for floating-point data.
 * @param[in] x  input value in radians.
 * @return  sin(x).
 */
float32_t dsp_sin_f32(
    float32_t x);





/**
 * @brief  Fast approximation to the trigonometric cosine function for floating-point data.
 * @param[in] x  input value in radians.
 * @return  cos(x).
 */
float32_t dsp_cos_f32(
    float32_t x);





/**
 * @ingroup groupFastMath
 */


/**
 * @defgroup SQRT Square Root
 *
 * Computes the square root of a number.
 * There are separate functions for Q15, Q31, and floating-point data types.
 * The square root function is computed using the Newton-Raphson algorithm.
 * This is an iterative algorithm of the form:
 * <pre>
 *      x1 = x0 - f(x0)/f'(x0)
 * </pre>
 * where <code>x1</code> is the current estimate,
 * <code>x0</code> is the previous estimate, and
 * <code>f'(x0)</code> is the derivative of <code>f()</code> evaluated at <code>x0</code>.
 * For the square root function, the algorithm reduces to:
 * <pre>
 *     x0 = in/2                         [initial guess]
 *     x1 = 1/2 * ( x0 + in / x0)        [each iteration]
 * </pre>
 */


inline float invSqrt(float x)
{
    float halfx = 0.5f * x;
    float y = x;
    long i = *(long *)&y;
    i = 0x5f3759df - (i >> 1);
    y = *(float *)&i;
    y = y * (1.5f - (halfx * y * y));
    return y;
}

/**
 * @addtogroup SQRT
 * @{
 */

/**
 * @brief  Floating-point square root function.
 * @param[in]  in    input value.
 * @param[out] pOut  square root of input value.
 * @return The function returns dsp_MATH_SUCCESS if input value is positive value or dsp_MATH_ARGUMENT_ERROR if
 * <code>in</code> is negative value and returns zero output for negative values.
 */
static inline dsp_status dsp_sqrt_f32(
    float32_t in,
    float32_t *pOut)
{
    if (in >= 0.0f) {

#if   (__FPU_USED == 1) && defined ( __CC_DSP   )
        *pOut = __sqrtf(in);
#elif (__FPU_USED == 1) && (defined(__DSPCC_VERSION) && (__DSPCC_VERSION >= 6010050))
        *pOut = __builtin_sqrtf(in);
#elif (__FPU_USED == 1) && defined(__GNUC__)
        *pOut = __builtin_sqrtf(in);
#elif (__FPU_USED == 1) && defined ( __ICCDSP__ ) && (__VER__ >= 6040000)
        __ASM("VSQRT.F32 %0,%1" : "=t"(*pOut) : "t"(in));
#else
        // *pOut=invSqrt(in);
        // *pOut=1/(*pOut);
        *pOut = sqrtf(in);

#endif

        return (dsp_MATH_SUCCESS);
    } else {
        *pOut = 0.0f;
        return (dsp_MATH_ARGUMENT_ERROR);
    }
}




/**
 * @} end of SQRT group
 */


/**
 * @brief floating-point Circular write function.
 */
static inline void dsp_circularWrite_f32(
    int32_t *circBuffer,
    int32_t L,
    uint16_t *writeOffset,
    int32_t bufferInc,
    const int32_t *src,
    int32_t srcInc,
    uint32_t blockSize)
{
    uint32_t i = 0U;
    int32_t wOffset;

    /* Copy the value of Index pointer that points
     * to the current location where the input samples to be copied */
    wOffset = *writeOffset;

    /* Loop over the blockSize */
    i = blockSize;

    while (i > 0U) {
        /* copy the input sample to the circular buffer */
        circBuffer[wOffset] = *src;

        /* Update the input pointer */
        src += srcInc;

        /* Circularly update wOffset.  Watch out for positive and negative value */
        wOffset += bufferInc;

        if (wOffset >= L) {
            wOffset -= L;
        }

        /* Decrement the loop counter */
        i--;
    }

    /* Update the index pointer */
    *writeOffset = (uint16_t)wOffset;
}



/**
 * @brief floating-point Circular Read function.
 */
static inline void dsp_circularRead_f32(
    int32_t *circBuffer,
    int32_t L,
    int32_t *readOffset,
    int32_t bufferInc,
    int32_t *dst,
    int32_t *dst_base,
    int32_t dst_length,
    int32_t dstInc,
    uint32_t blockSize)
{
    uint32_t i = 0U;
    int32_t rOffset, dst_end;

    /* Copy the value of Index pointer that points
     * to the current location from where the input samples to be read */
    rOffset = *readOffset;
    dst_end = (int32_t)(dst_base + dst_length);

    /* Loop over the blockSize */
    i = blockSize;

    while (i > 0U) {
        /* copy the sample from the circular buffer to the destination buffer */
        *dst = circBuffer[rOffset];

        /* Update the input pointer */
        dst += dstInc;

        if (dst == (int32_t *) dst_end) {
            dst = dst_base;
        }

        /* Circularly update rOffset.  Watch out for positive and negative value  */
        rOffset += bufferInc;

        if (rOffset >= L) {
            rOffset -= L;
        }

        /* Decrement the loop counter */
        i--;
    }

    /* Update the index pointer */
    *readOffset = rOffset;
}





/**
 * @brief  Sum of the squares of the elements of a floating-point vector.
 * @param[in]  pSrc       is input pointer
 * @param[in]  blockSize  is the number of samples to process
 * @param[out] pResult    is output value.
 */
void dsp_power_f32(
    float32_t *pSrc,
    uint32_t blockSize,
    float32_t *pResult);





/**
 * @brief  Mean value of a floating-point vector.
 * @param[in]  pSrc       is input pointer
 * @param[in]  blockSize  is the number of samples to process
 * @param[out] pResult    is output value.
 */
void dsp_mean_f32(
    float32_t *pSrc,
    uint32_t blockSize,
    float32_t *pResult);


/**
 * @brief  Variance of the elements of a floating-point vector.
 * @param[in]  pSrc       is input pointer
 * @param[in]  blockSize  is the number of samples to process
 * @param[out] pResult    is output value.
 */
void dsp_var_f32(
    float32_t *pSrc,
    uint32_t blockSize,
    float32_t *pResult);





/**
 * @brief  Root Mean Square of the elements of a floating-point vector.
 * @param[in]  pSrc       is input pointer
 * @param[in]  blockSize  is the number of samples to process
 * @param[out] pResult    is output value.
 */
void dsp_rms_f32(
    float32_t *pSrc,
    uint32_t blockSize,
    float32_t *pResult);





/**
 * @brief  Standard deviation of the elements of a floating-point vector.
 * @param[in]  pSrc       is input pointer
 * @param[in]  blockSize  is the number of samples to process
 * @param[out] pResult    is output value.
 */
void dsp_std_f32(
    float32_t *pSrc,
    uint32_t blockSize,
    float32_t *pResult);





/**
 * @brief  Floating-point complex magnitude
 * @param[in]  pSrc        points to the complex input vector
 * @param[out] pDst        points to the real output vector
 * @param[in]  numSamples  number of complex samples in the input vector
 */
void dsp_cmplx_mag_f32(
    float32_t *pSrc,
    float32_t *pDst,
    uint32_t numSamples);





/**
 * @brief  Floating-point complex dot product
 * @param[in]  pSrcA       points to the first input vector
 * @param[in]  pSrcB       points to the second input vector
 * @param[in]  numSamples  number of complex samples in each vector
 * @param[out] realResult  real part of the result returned here
 * @param[out] imagResult  imaginary part of the result returned here
 */
void dsp_cmplx_dot_prod_f32(
    float32_t *pSrcA,
    float32_t *pSrcB,
    uint32_t numSamples,
    float32_t *realResult,
    float32_t *imagResult);








/**
 * @brief  Floating-point complex-by-real multiplication
 * @param[in]  pSrcCmplx   points to the complex input vector
 * @param[in]  pSrcReal    points to the real input vector
 * @param[out] pCmplxDst   points to the complex output vector
 * @param[in]  numSamples  number of samples in each vector
 */
void dsp_cmplx_mult_real_f32(
    float32_t *pSrcCmplx,
    float32_t *pSrcReal,
    float32_t *pCmplxDst,
    uint32_t numSamples);





/**
 * @brief  Minimum value of a floating-point vector.
 * @param[in]  pSrc       is input pointer
 * @param[in]  blockSize  is the number of samples to process
 * @param[out] pResult    is output pointer
 * @param[out] pIndex     is the array index of the minimum value in the input buffer.
 */
void dsp_min_f32(
    float32_t *pSrc,
    uint32_t blockSize,
    float32_t *pResult,
    uint32_t *pIndex);




/**
 * @brief Maximum value of a floating-point vector.
 * @param[in]  pSrc       points to the input buffer
 * @param[in]  blockSize  length of the input vector
 * @param[out] pResult    maximum value returned here
 * @param[out] pIndex     index of maximum value returned here
 */
void dsp_max_f32(
    float32_t *pSrc,
    uint32_t blockSize,
    float32_t *pResult,
    uint32_t *pIndex);





/**
 * @brief  Floating-point complex-by-complex multiplication
 * @param[in]  pSrcA       points to the first input vector
 * @param[in]  pSrcB       points to the second input vector
 * @param[out] pDst        points to the output vector
 * @param[in]  numSamples  number of complex samples in each vector
 */
void dsp_cmplx_mult_cmplx_f32(
    float32_t *pSrcA,
    float32_t *pSrcB,
    float32_t *pDst,
    uint32_t numSamples);





/**components/unity/
 * @ingroup groupInterpolation
 */

/**
 * @defgroup BilinearInterpolate Bilinear Interpolation
 *
 * Bilinear interpolation is an extension of linear interpolation applied to a two dimensional grid.
 * The underlying function <code>f(x, y)</code> is sampled on a regular grid and the interpolation process
 * determines values between the grid points.
 * Bilinear interpolation is equivalent to two step linear interpolation, first in the x-dimension and then in the y-dimension.
 * Bilinear interpolation is often used in image processing to rescale images.
 * The CMSIS DSP library provides bilinear interpolation functions for Q7, Q15, Q31, and floating-point data types.
 *
 * <b>Algorithm</b>
 * \par
 * The instance structure used by the bilinear interpolation functions describes a two dimensional data table.
 * For floating-point, the instance structure is defined as:
 * <pre>
 *   typedef struct
 *   {
 *     uint16_t numRows;
 *     uint16_t numCols;
 *     float32_t *pData;
 * } dsp_bilinear_interp_instance_f32;
 * </pre>
 *
 * \par
 * where <code>numRows</code> specifies the number of rows in the table;
 * <code>numCols</code> specifies the number of columns in the table;
 * and <code>pData</code> points to an array of size <code>numRows*numCols</code> values.
 * The data table <code>pTable</code> is organized in row order and the supplied data values fall on integer indexes.
 * That is, table element (x,y) is located at <code>pTable[x + y*numCols]</code> where x and y are integers.
 *
 * \par
 * Let <code>(x, y)</code> specify the desired interpolation point.  Then define:
 * <pre>
 *     XF = floor(x)
 *     YF = floor(y)
 * </pre>
 * \par
 * The interpolated output point is computed as:
 * <pre>
 *  f(x, y) = f(XF, YF) * (1-(x-XF)) * (1-(y-YF))
 *           + f(XF+1, YF) * (x-XF)*(1-(y-YF))
 *           + f(XF, YF+1) * (1-(x-XF))*(y-YF)
 *           + f(XF+1, YF+1) * (x-XF)*(y-YF)
 * </pre>
 * Note that the coordinates (x, y) contain integer and fractional components.
 * The integer components specify which portion of the table to use while the
 * fractional components control the interpolation processor.
 *
 * \par
 * if (x,y) are outside of the table boundary, Bilinear interpolation returns zero output.
 */

/**
 * @addtogroup BilinearInterpolate
 * @{
 */


/**
*
* @brief  Floating-point bilinear interpolation.
* @param[in,out] S  points to an instance of the interpolation structure.
* @param[in]     X  interpolation coordinate.
* @param[in]     Y  interpolation coordinate.
* @return out interpolated value.
*/
static inline float32_t dsp_bilinear_interp_f32(
    const dsp_bilinear_interp_instance_f32 *S,
    float32_t X,
    float32_t Y)
{
    float32_t out;
    float32_t f00, f01, f10, f11;
    float32_t *pData = S->pData;
    int32_t xIndex, yIndex, index;
    float32_t xdiff, ydiff;
    float32_t b1, b2, b3, b4;

    xIndex = (int32_t) X;
    yIndex = (int32_t) Y;

    /* Care taken for table outside boundary */
    /* Returns zero output when values are outside table boundary */
    if (xIndex < 0 || xIndex > (S->numRows - 1) || yIndex < 0 || yIndex > (S->numCols - 1)) {
        return (0);
    }

    /* Calculation of index for two nearest points in X-direction */
    index = (xIndex - 1) + (yIndex - 1) * S->numCols;


    /* Read two nearest points in X-direction */
    f00 = pData[index];
    f01 = pData[index + 1];

    /* Calculation of index for two nearest points in Y-direction */
    index = (xIndex - 1) + (yIndex) * S->numCols;


    /* Read two nearest points in Y-direction */
    f10 = pData[index];
    f11 = pData[index + 1];

    /* Calculation of intermediate values */
    b1 = f00;
    b2 = f01 - f00;
    b3 = f10 - f00;
    b4 = f00 - f01 - f10 + f11;

    /* Calculation of fractional part in X */
    xdiff = X - xIndex;

    /* Calculation of fractional part in Y */
    ydiff = Y - yIndex;

    /* Calculation of bi-linear interpolated output */
    out = b1 + b2 * xdiff + b3 * ydiff + b4 * xdiff * ydiff;

    /* return to application */
    return (out);
}







#if   defined ( __CC_DSP )
/* Enter low optimization region - place directly above function definition */
#if defined( DSP_MATH_CM4 ) || defined( DSP_MATH_CM7)
#define LOW_OPTIMIZATION_ENTER \
    _Pragma ("push")         \
    _Pragma ("O1")
#else
#define LOW_OPTIMIZATION_ENTER
#endif

/* Exit low optimization region - place directly after end of function definition */
#if defined ( DSP_MATH_CM4 ) || defined ( DSP_MATH_CM7 )
#define LOW_OPTIMIZATION_EXIT \
    _Pragma ("pop")
#else
#define LOW_OPTIMIZATION_EXIT
#endif

/* Enter low optimization region - place directly above function definition */
#define IAR_ONLY_LOW_OPTIMIZATION_ENTER

/* Exit low optimization region - place directly after end of function definition */
#define IAR_ONLY_LOW_OPTIMIZATION_EXIT

#elif defined (__DSPCC_VERSION ) && ( __DSPCC_VERSION >= 6010050 )
#define LOW_OPTIMIZATION_ENTER
#define LOW_OPTIMIZATION_EXIT
#define IAR_ONLY_LOW_OPTIMIZATION_ENTER
#define IAR_ONLY_LOW_OPTIMIZATION_EXIT

#elif defined ( __GNUC__ )
#define LOW_OPTIMIZATION_ENTER \
    __attribute__(( optimize("-O1") ))
#define LOW_OPTIMIZATION_EXIT
#define IAR_ONLY_LOW_OPTIMIZATION_ENTER
#define IAR_ONLY_LOW_OPTIMIZATION_EXIT

#elif defined ( __ICCDSP__ )
/* Enter low optimization region - place directly above function definition */
#if defined ( DSP_MATH_CM4 ) || defined ( DSP_MATH_CM7 )
#define LOW_OPTIMIZATION_ENTER \
    _Pragma ("optimize=low")
#else
#define LOW_OPTIMIZATION_ENTER
#endif

/* Exit low optimization region - place directly after end of function definition */
#define LOW_OPTIMIZATION_EXIT

/* Enter low optimization region - place directly above function definition */
#if defined ( DSP_MATH_CM4 ) || defined ( DSP_MATH_CM7 )
#define IAR_ONLY_LOW_OPTIMIZATION_ENTER \
    _Pragma ("optimize=low")
#else
#define IAR_ONLY_LOW_OPTIMIZATION_ENTER
#endif

/* Exit low optimization region - place directly after end of function definition */
#define IAR_ONLY_LOW_OPTIMIZATION_EXIT

#elif defined ( __TI_DSP__ )
#define LOW_OPTIMIZATION_ENTER
#define LOW_OPTIMIZATION_EXIT
#define IAR_ONLY_LOW_OPTIMIZATION_ENTER
#define IAR_ONLY_LOW_OPTIMIZATION_EXIT

#elif defined ( __CSMC__ )
#define LOW_OPTIMIZATION_ENTER
#define LOW_OPTIMIZATION_EXIT
#define IAR_ONLY_LOW_OPTIMIZATION_ENTER
#define IAR_ONLY_LOW_OPTIMIZATION_EXIT

#elif defined ( __TASKING__ )
#define LOW_OPTIMIZATION_ENTER
#define LOW_OPTIMIZATION_EXIT
#define IAR_ONLY_LOW_OPTIMIZATION_ENTER
#define IAR_ONLY_LOW_OPTIMIZATION_EXIT

#endif


#ifdef   __cplusplus
}
#endif

/* Compiler specific diagnostic adjustment */
#if   defined ( __CC_DSP )

#elif defined ( __DSPCC_VERSION ) && ( __DSPCC_VERSION >= 6010050 )

#elif defined ( __GNUC__ )
#pragma GCC diagnostic pop

#elif defined ( __ICCDSP__ )

#elif defined ( __TI_DSP__ )

#elif defined ( __CSMC__ )

#elif defined ( __TASKING__ )

#else
#error Unknown compiler
#endif
