ATmega8/kiterf/project/code/ESP32/Demo/components/dsp/include/dsp_const_structs.h

#pragma once

#include "dsp_math.h"
#include "dsp_common_tables.h"

#ifdef __cplusplus
extern "C" {
#endif

extern const dsp_cfft_instance_f32 dsp_cfft_sR_f32_len16;
extern const dsp_cfft_instance_f32 dsp_cfft_sR_f32_len32;
extern const dsp_cfft_instance_f32 dsp_cfft_sR_f32_len64;
extern const dsp_cfft_instance_f32 dsp_cfft_sR_f32_len128;
extern const dsp_cfft_instance_f32 dsp_cfft_sR_f32_len256;
extern const dsp_cfft_instance_f32 dsp_cfft_sR_f32_len512;
extern const dsp_cfft_instance_f32 dsp_cfft_sR_f32_len1024;
extern const dsp_cfft_instance_f32 dsp_cfft_sR_f32_len2048;
extern const dsp_cfft_instance_f32 dsp_cfft_sR_f32_len4096;

#ifdef __cplusplus
}
#endif
